dcasati/morsebridge/MorseBridge/BlePaddleKeyboard.h

#pragma once

#include <stdint.h>

namespace MorseBle {

enum class Status { Waiting, Connecting, ReleasePaddles, Ready, UsbReady, Error };

struct Diagnostics {
  bool connected;
  bool authenticated;
  bool subscribed;
  bool suspended;
  bool armed;
  uint32_t queuedReports;
  uint8_t lastQueuedModifiers;
};

bool begin();
void update(bool ditDown, bool dahDown, bool selected = true);
bool released();
bool end();
Status status();
Diagnostics diagnostics();

}
